ScatteredDrifter/Stucco_15-10/pcb_stucco/kb_matrix.kicad_sch

## KiCad design pcb_stucco/kb_matrix.kicad_sch (2023-12-31)

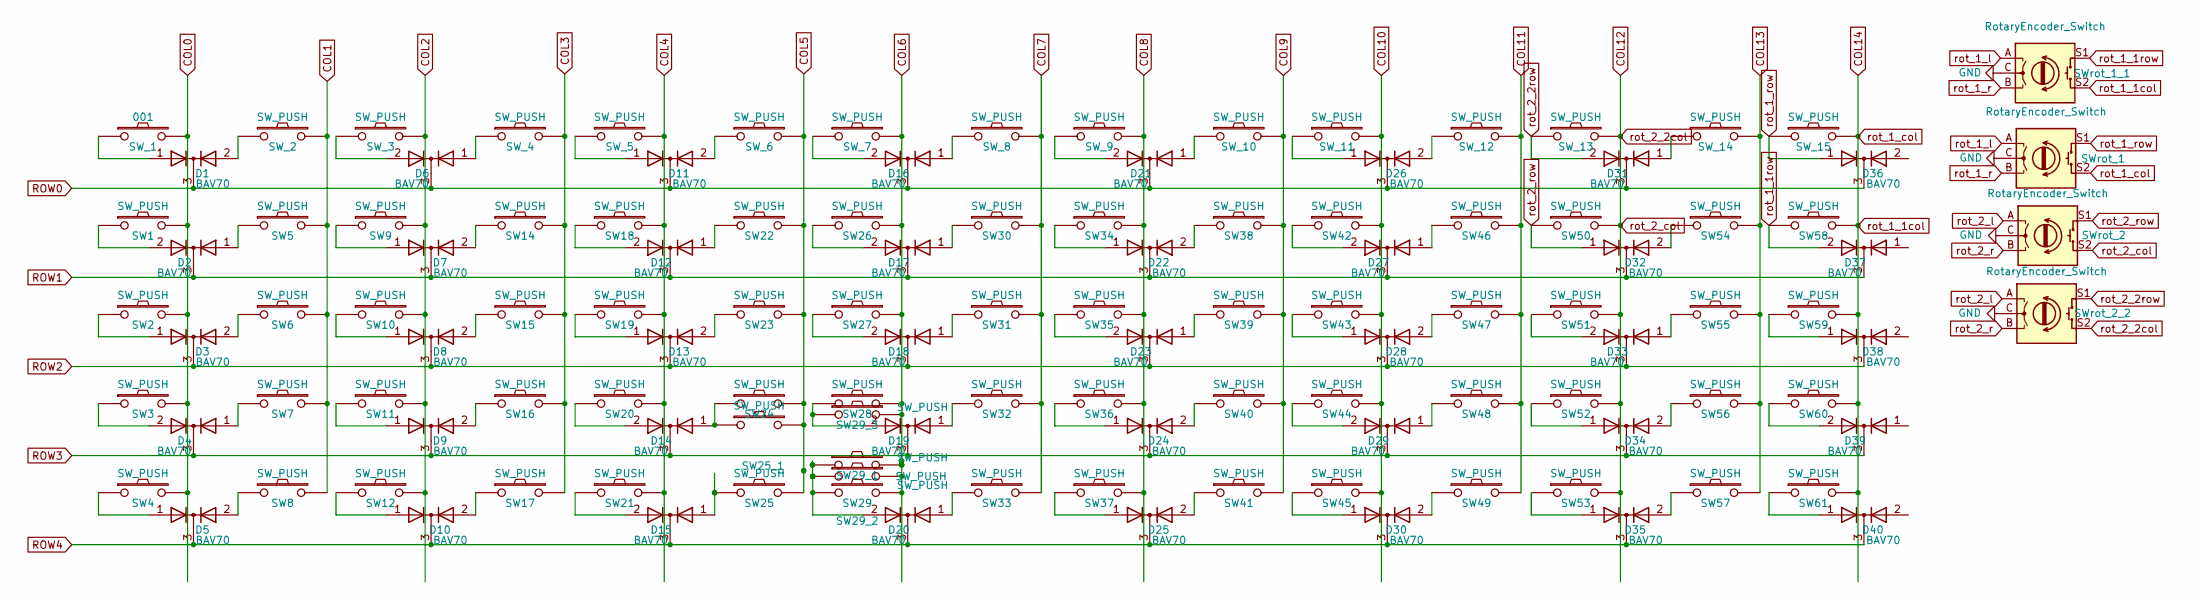
[picture p5: schematic kb_matrix.kicad_sch]

Parts:
D1, D2, D3, D4, D5, D6, D7, D8, D9, D10, D11, D12, D13, D14, D15, D16, D17, D18, D19, D20, D21, D22, D23, D24, D25, D26, D27, D28, D29, D30, D31, D32, D33, D34, D35, D36, D37, D38, D39, D40: BAV70; SOT-23; LCSC C68978
SW1, SW2, SW3, SW4, SW5, SW6, SW7, SW8, SW9, SW10, SW11, SW12, SW14, SW15, SW16, SW17, SW18, SW19, SW20, SW21, SW22, SW23, SW24, SW25, SW25_1, SW26, SW27, SW28, SW29, SW29_1, SW29_2, SW29_3, SW30, SW31, SW32, SW33, SW34, SW35, SW36, SW37, SW38, SW39, SW40, SW41, SW42, SW43, SW44, SW45, SW46, SW47, SW48, SW49, SW50, SW51, SW52, SW53, SW54, SW55, SW56, SW57, SW58, SW59, SW60, SW61: SW_PUSH; SW_MX_1u
SW_1: 001; SW_MX_1u
SW_2, SW_3, SW_4, SW_5, SW_6, SW_7, SW_8, SW_9, SW_10, SW_11, SW_12, SW_13, SW_14, SW_15: SW_PUSH; SW_MX_1u
SWrot_1, SWrot_1_1, SWrot_2, SWrot_2_2: RotaryEncoder_Switch; RotaryEncoder_EC11

Connections:
COL0: SW1.2, SW2.2, SW3.2, SW4.2, SW_1.2
COL1: SW5.2, SW6.2, SW7.2, SW8.2, SW_2.2
COL2: SW9.2, SW10.2, SW11.2, SW12.2, SW_3.2
COL3: SW14.2, SW15.2, SW16.2, SW17.2, SW_4.2
COL4: SW18.2, SW19.2, SW20.2, SW21.2, SW_5.2
COL5: SW22.2, SW23.2, SW24.2, SW25.2, SW25_1.2, SW_6.2
COL6: SW26.2, SW27.2, SW28.2, SW29.2, SW29_1.2, SW29_2.2, SW29_3.2, SW_7.2
COL7: SW30.2, SW31.2, SW32.2, SW33.2, SW_8.2
COL8: SW34.2, SW35.2, SW36.2, SW37.2, SW_9.2
COL9: SW38.2, SW39.2, SW40.2, SW41.2, SW_10.2
COL10: SW42.2, SW43.2, SW44.2, SW45.2, SW_11.2
COL11: SW46.2, SW47.2, SW48.2, SW49.2, SW_12.2
COL12: SW50.2, SW51.2, SW52.2, SW53.2, SW_13.2, SWrot_2.S2, SWrot_2_2.S2
COL13: SW54.2, SW55.2, SW56.2, SW57.2, SW_14.2
COL14: SW58.2, SW59.2, SW60.2, SW61.2, SW_15.2, SWrot_1.S2, SWrot_1_1.S2
GND: SWrot_1.C, SWrot_1_1.C, SWrot_2.C, SWrot_2_2.C
unnamed: D1.1 (A), SW_1.1
unnamed: D1.2 (A), SW_2.1
unnamed: D2.1 (A), SW5.1
unnamed: D2.2 (A), SW1.1
unnamed: D3.1 (A), SW2.1
unnamed: D3.2 (A), SW6.1
unnamed: D4.1 (A), SW7.1
unnamed: D4.2 (A), SW3.1
unnamed: D5.1 (A), SW4.1
unnamed: D5.2 (A), SW8.1
unnamed: D6.1 (A), SW_4.1
unnamed: D6.2 (A), SW_3.1
unnamed: D7.1 (A), SW9.1
unnamed: D7.2 (A), SW14.1
unnamed: D8.1 (A), SW10.1
unnamed: D8.2 (A), SW15.1
unnamed: D9.1 (A), SW11.1
unnamed: D9.2 (A), SW16.1
unnamed: D10.1 (A), SW12.1
unnamed: D10.2 (A), SW17.1
unnamed: D11.1 (A), SW_5.1
unnamed: D11.2 (A), SW_6.1
unnamed: D12.1 (A), SW22.1
unnamed: D12.2 (A), SW18.1
unnamed: D13.1 (A), SW19.1
unnamed: D13.2 (A), SW23.1
unnamed: D14.1 (A), SW24.1, SW25_1.1
unnamed: D14.2 (A), SW20.1
unnamed: D15.1 (A), SW25.1
unnamed: D15.2 (A), SW21.1
unnamed: D16.1 (A), SW_8.1
unnamed: D16.2 (A), SW_7.1
unnamed: D17.1 (A), SW30.1
unnamed: D17.2 (A), SW26.1
unnamed: D18.1 (A), SW31.1
unnamed: D18.2 (A), SW27.1
unnamed: D19.1 (A), SW32.1
unnamed: D19.2 (A), SW28.1, SW29_3.1
unnamed: D20.1 (A), SW33.1
unnamed: D20.2 (A), SW29.1, SW29_1.1, SW29_2.1
unnamed: D21.1 (A), SW_10.1
unnamed: D21.2 (A), SW_9.1
unnamed: D22.1 (A), SW34.1
unnamed: D22.2 (A), SW38.1
unnamed: D23.1 (A), SW39.1
unnamed: D23.2 (A), SW35.1
unnamed: D24.1 (A), SW36.1
unnamed: D24.2 (A), SW40.1
unnamed: D25.1 (A), SW37.1
unnamed: D25.2 (A), SW41.1
unnamed: D26.1 (A), SW_11.1
unnamed: D26.2 (A), SW_12.1
unnamed: D27.1 (A), SW46.1
unnamed: D27.2 (A), SW42.1
unnamed: D28.1 (A), SW43.1
unnamed: D28.2 (A), SW47.1
unnamed: D29.1 (A), SW48.1
unnamed: D29.2 (A), SW44.1
unnamed: D30.1 (A), SW45.1
unnamed: D30.2 (A), SW49.1
unnamed: D31.1 (A), SW_14.1
unnamed: D32.2 (A), SW54.1
unnamed: D33.1 (A), SW55.1
unnamed: D33.2 (A), SW51.1
unnamed: D34.1 (A), SW52.1
unnamed: D34.2 (A), SW56.1
unnamed: D35.1 (A), SW53.1
unnamed: D35.2 (A), SW57.1
unnamed: D38.1 (A), SW59.1
unnamed: D39.2 (A), SW60.1
unnamed: D40.1 (A), SW61.1
ROW0: D1.3 (K), D6.3 (K), D11.3 (K), D16.3 (K), D21.3 (K), D26.3 (K), D31.3 (K), D36.3 (K)
ROW1: D2.3 (K), D7.3 (K), D12.3 (K), D17.3 (K), D22.3 (K), D27.3 (K), D32.3 (K), D37.3 (K)
ROW2: D3.3 (K), D8.3 (K), D13.3 (K), D18.3 (K), D23.3 (K), D28.3 (K), D33.3 (K), D38.3 (K)
ROW3: D4.3 (K), D9.3 (K), D14.3 (K), D19.3 (K), D24.3 (K), D29.3 (K), D34.3 (K), D39.3 (K)
ROW4: D5.3 (K), D10.3 (K), D15.3 (K), D20.3 (K), D25.3 (K), D30.3 (K), D35.3 (K), D40.3 (K)
rot_1_1row: D37.2 (A), SW58.1, SWrot_1_1.S1
rot_1_l: SWrot_1.A, SWrot_1_1.A
rot_1_r: SWrot_1.B, SWrot_1_1.B
rot_1_row: D36.1 (A), SW_15.1, SWrot_1.S1
rot_2_2row: D31.2 (A), SW_13.1, SWrot_2_2.S1
rot_2_l: SWrot_2.A, SWrot_2_2.A
rot_2_r: SWrot_2.B, SWrot_2_2.B
rot_2_row: D32.1 (A), SW50.1, SWrot_2.S1
