ScatteredDrifter/Stucco_15-10/pcb_stucco/.32u2_version/32u2.kicad_sch

## KiCad design pcb_stucco/.32u2_version/32u2.kicad_sch (2023-12-31)

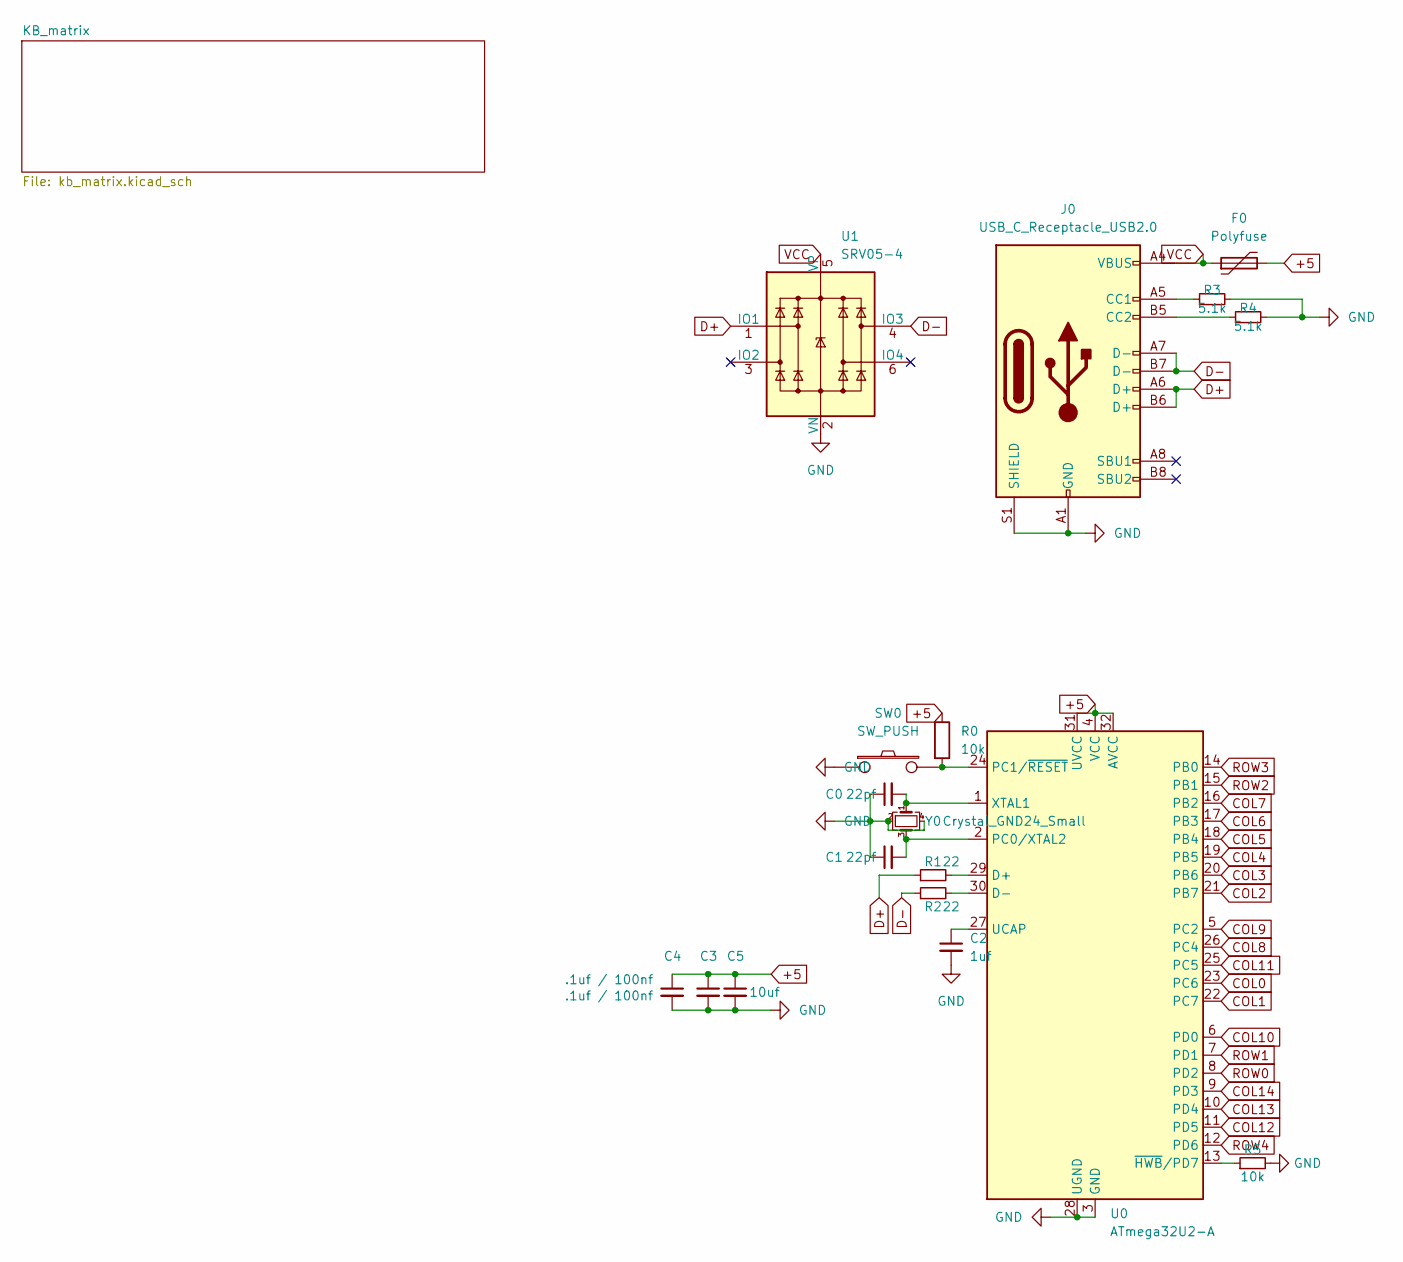
[picture p7: schematic 32u2.kicad_sch]

Parts:
C0, C1: 22pf; C_0805_2012Metric; LCSC C1804
C2: 1uf; C_0805_2012Metric; LCSC C28323
C3, C4: .1uf / 100nf; C_0805_2012Metric; LCSC C49678
C5: 10uf; R_0805_2012Metric; LCSC C91245
F0: Polyfuse; R_0805_2012Metric; LCSC C69688
J0: USB_C_Receptacle_USB2.0; USB_C_Receptacle_HRO_TYPE-C-31-M-12; LCSC C165948
R0, R5: 10k; R_0805_2012Metric; LCSC C17414
R1, R2: 22; R_0805_2012Metric; LCSC C17561
R3, R4: 5.1k; R_0805_2012Metric; LCSC C27834
SW0: SW_PUSH; SW_SPST_TL3342; LCSC C318884
U0: ATmega32U2-A; TQFP-32_7x7mm_P0.8mm; LCSC C618733
U1: SRV05-4; SOT-23-6; LCSC C85364
Y0: Crystal_GND24_Small; Crystal_SMD_3225-4Pin_3.2x2.5mm; LCSC C13738

Connections:
+5: C3.1, C4.1, C5.1, F0.2, R0.1, U0.4 (VCC), U0.31 (UVCC), U0.32 (AVCC)
COL0: U0.23 (PC6)
COL1: U0.22 (PC7)
COL2: U0.21 (PB7)
COL3: U0.20 (PB6)
COL4: U0.19 (PB5)
COL5: U0.18 (PB4)
COL6: U0.17 (PB3)
COL7: U0.16 (PB2)
COL8: U0.26 (PC4)
COL9: U0.5 (PC2)
COL10: U0.6 (PD0)
COL11: U0.25 (PC5)
COL12: U0.11 (PD5)
COL13: U0.10 (PD4)
COL14: U0.9 (PD3)
D+: J0.A6 (D+), J0.B6 (D+), R1.1, U1.1 (IO1)
D-: J0.A7 (D-), J0.B7 (D-), R2.1, U1.4 (IO3)
GND: C0.1, C1.1, C2.2, C3.2, C4.2, C5.2, J0.A1 (GND), J0.A12 (GND), J0.B1 (GND), J0.B12 (GND), J0.S1 (SHIELD), R3.2, R4.2, R5.2, SW0.1, U0.3 (GND), U0.28 (UGND), U1.2 (VN), Y0.2, Y0.4
unnamed: C0.2, U0.1 (XTAL1), Y0.1
unnamed: C1.2, U0.2 (PC0/XTAL2), Y0.3
unnamed: C2.1, U0.27 (UCAP)
unnamed: J0.A5 (CC1), R3.1
unnamed: J0.B5 (CC2), R4.1
unnamed: R0.2, SW0.2, U0.24 (PC1/~RESET)
unnamed: R1.2, U0.29 (D+)
unnamed: R2.2, U0.30 (D-)
unnamed: R5.1, U0.13 (~HWB/PD7)
ROW0: U0.8 (PD2)
ROW1: U0.7 (PD1)
ROW2: U0.15 (PB1)
ROW3: U0.14 (PB0)
ROW4: U0.12 (PD6)
VCC: F0.1, J0.A4 (VBUS), J0.A9 (VBUS), J0.B4 (VBUS), J0.B9 (VBUS), U1.5 (VP)
